mintlabkorea/open-source-ankle-exoskeleton/CAD_image/Bearing Sample.PNG

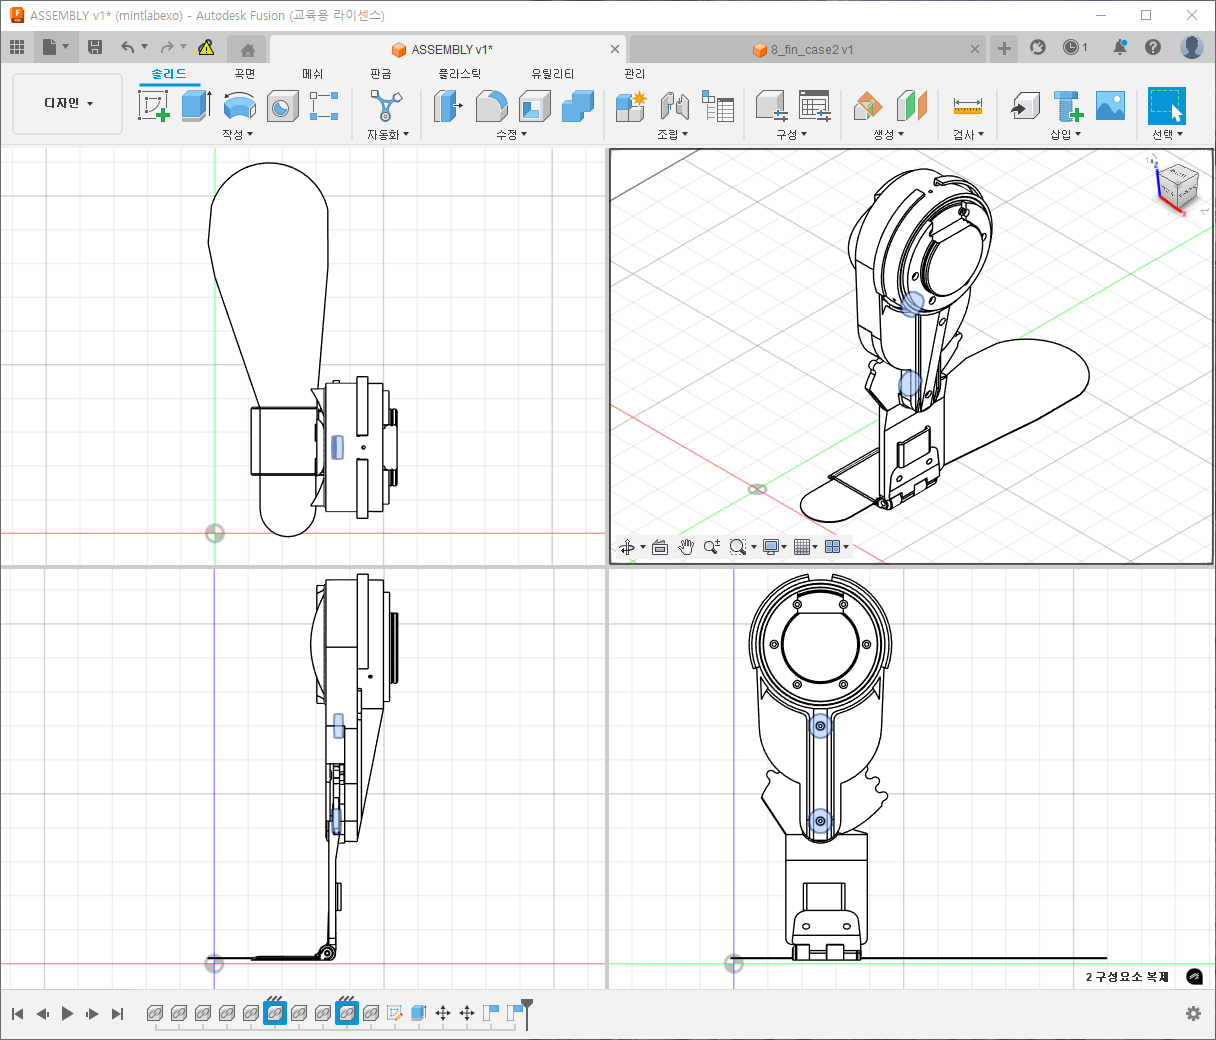
CAD_image/Bearing Sample.PNG
